OAMK-Smart-Kitchen/Smart-Fridge-OAMK/SmartKitchen-Emdebbed System/Datasheets/BL-LS1311-smd-led-lamp.gif

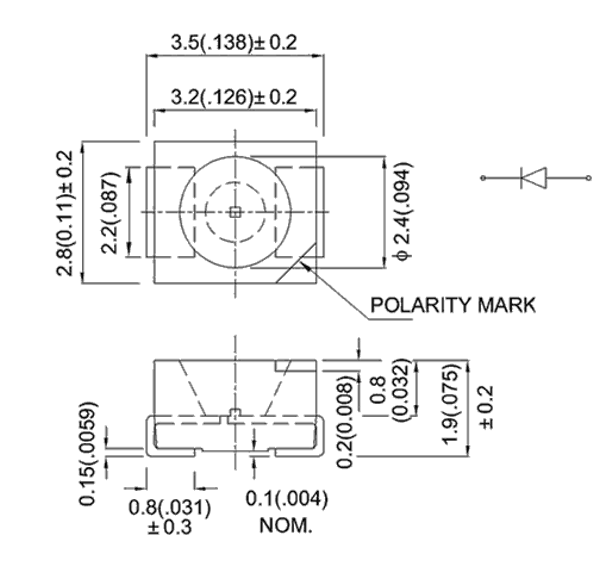
SmartKitchen-Emdebbed System/Datasheets/BL-LS1311-smd-led-lamp.gif
