OAMK-Smart-Kitchen/Smart-Fridge-OAMK/SmartKitchenApp/Documentation/Demo Screens/Dashboard_iPad_Black.png

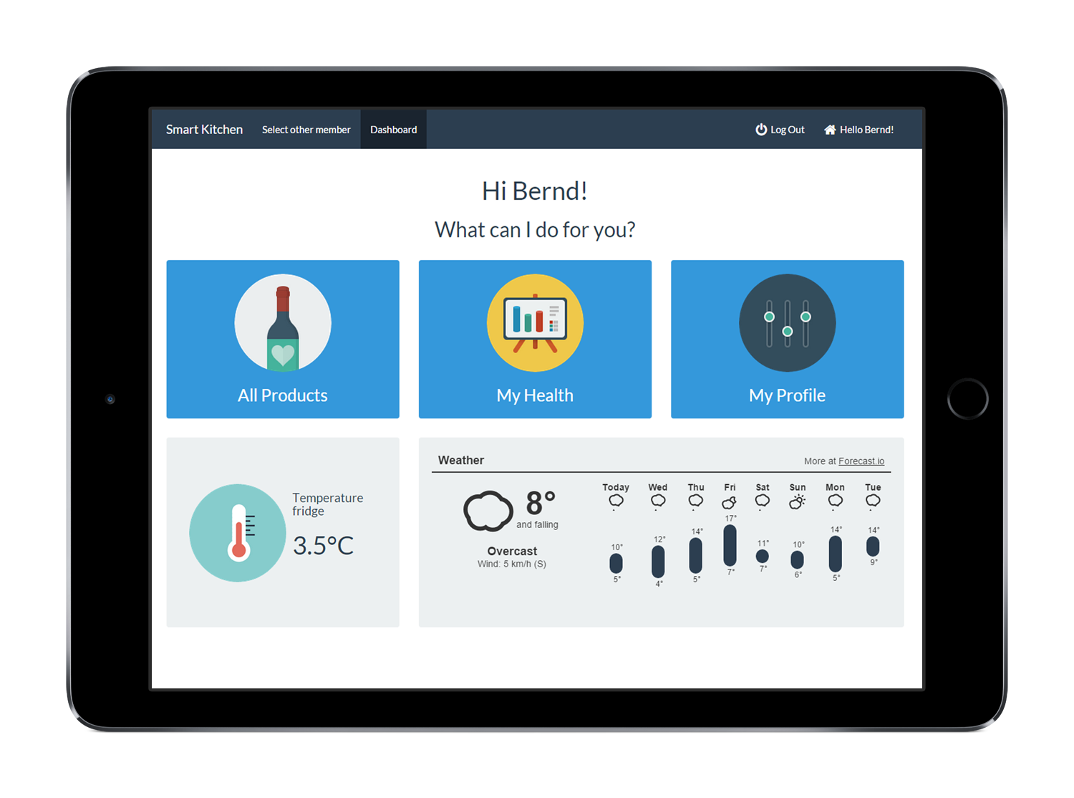
SmartKitchenApp/Documentation/Demo Screens/Dashboard_iPad_Black.png
