OAMK-Smart-Kitchen/Smart-Fridge-OAMK/SmartKitchenApp/Documentation/Demo Screens/My_Health_iPad_Black.png

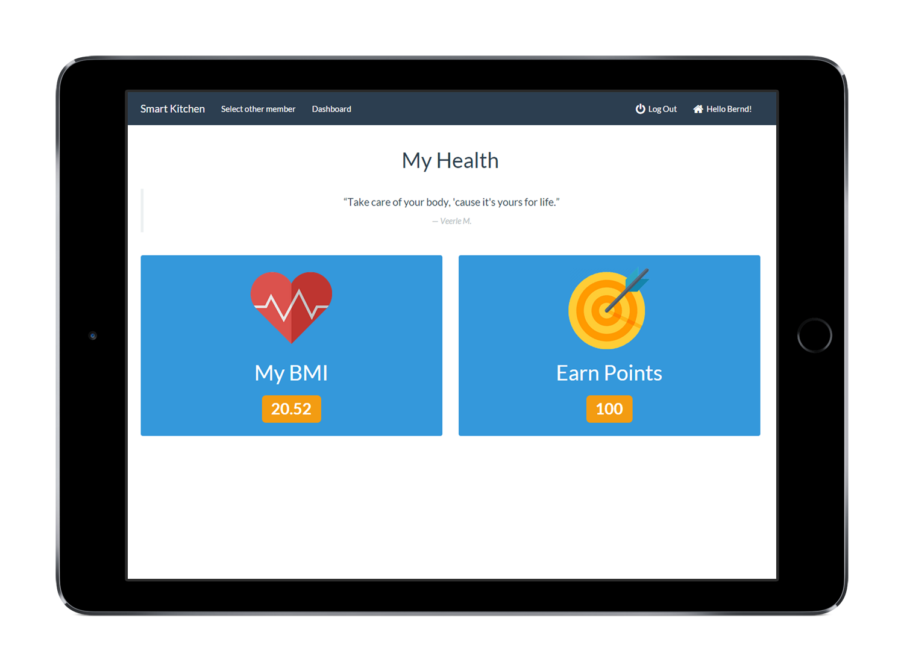
SmartKitchenApp/Documentation/Demo Screens/My_Health_iPad_Black.png
