OAMK-Smart-Kitchen/Smart-Fridge-OAMK/SmartKitchenApp/Documentation/Demo Screens/Points_iPad_Black.png

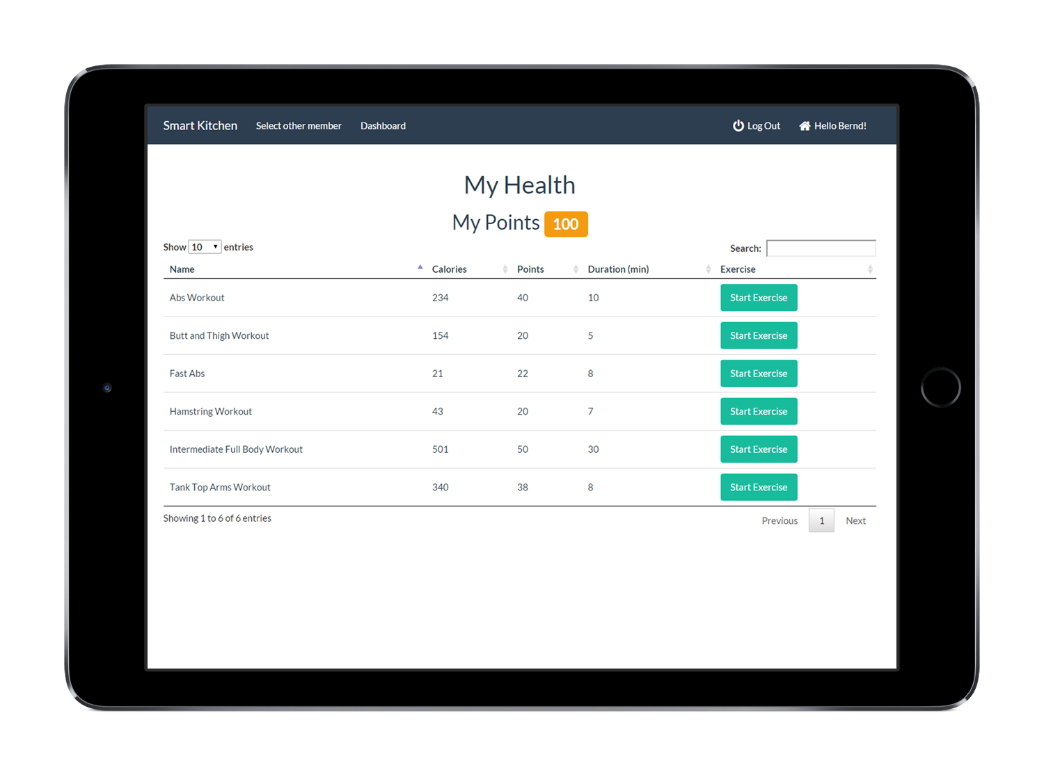
SmartKitchenApp/Documentation/Demo Screens/Points_iPad_Black.png
