OAMK-Smart-Kitchen/Smart-Fridge-OAMK/SmartKitchenApp/Documentation/Demo Screens/Workout_Video_iPad_Black.png

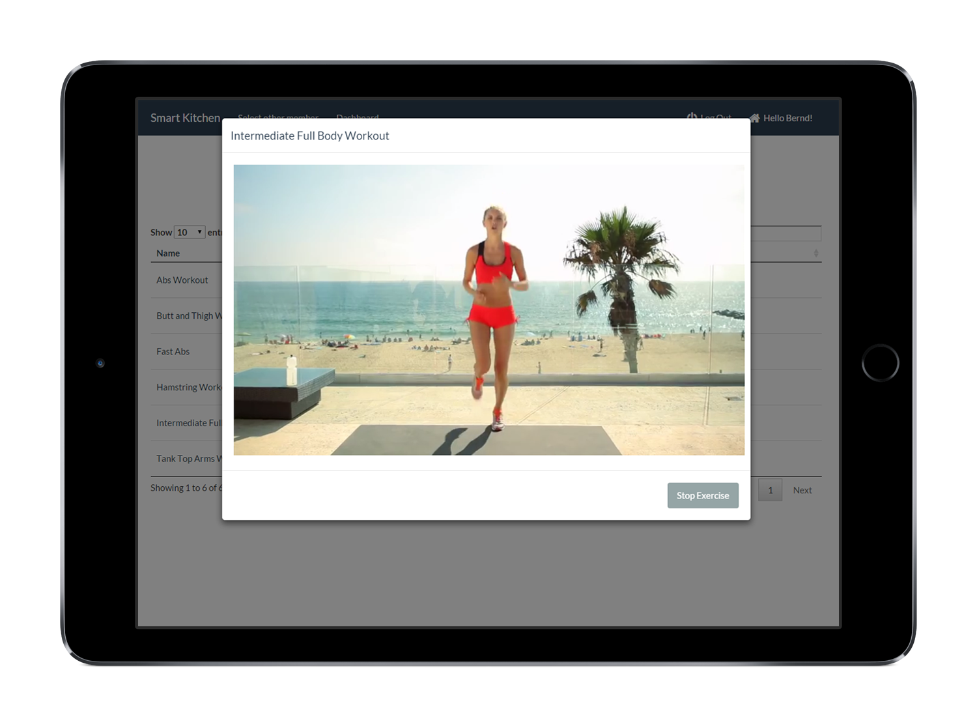
SmartKitchenApp/Documentation/Demo Screens/Workout_Video_iPad_Black.png
