OAMK-Smart-Kitchen/Smart-Fridge-OAMK/SmartKitchen-Emdebbed System/Hardware/Components/Capture.JPG

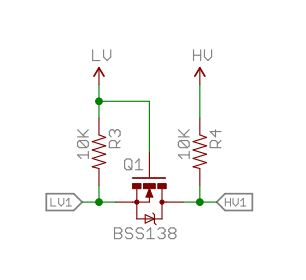
SmartKitchen-Emdebbed System/Hardware/Components/Capture.JPG
