OAMK-Smart-Kitchen/Smart-Fridge-OAMK/SmartKitchen-Emdebbed System/Software/Arduino/CommunicationtestARD/Test with SoftSerial/Test_Softserial_write.ino/Test_Softserial_write.ino.ino

/*
Uses a FOR loop for data and prints a number in various formats.
*/
int x = 0;    // variable

void setup() {
  Serial.begin(9600);      // open the serial port at 9600 bps:    
}

void loop() {  
  // print labels 
  Serial.print("XD48525352706548656557515256481310DA14ABtrueBX"); // a = 97 b = 98

  
    delay(200);            // delay 200 milliseconds

}
