OAMK-Smart-Kitchen/Smart-Fridge-OAMK/SmartKitchen-Emdebbed System/Software/Arduino/I2C_Tests/Working_I2C_2xPCF/Working_I2C_2xPCF.ino

#include <Wire.h>
 
byte iInput=0;
byte iOutput=0;
 
void setup()
{
  Wire.begin();
  Serial.begin(9600);
   pinMode(13, OUTPUT);
}
 
void loop()
{
  Wire.requestFrom(57,1);// Begin transmission to PCF8574 with the buttons (address: 111001)
  if(Wire.available())   // If bytes are available to be recieved
  {
    iInput = Wire.read();// Read a byte
    Serial.println(iInput);
  }
 
  if(iInput<=255)         //If the value less than 255
  {
    
    if (iInput==254) // P0
    { 
      iOutput = 1; 
    }; 
    if (iInput==253) // P1
    { 
      iOutput = 2; 
    }; 
    if (iInput==251) // P2
    { 
      iOutput = 4; 
    }; 
    if (iInput==247) // P3
    { 
      iOutput = 9; 
    };
    if (iInput==222) // P3
    { 
      iOutput = 9; 
    };
    
  }
  Wire.beginTransmission(56);  //Begin transmission to PCF8574 (with the LEDs)(address: 111000)
  Wire.write(iOutput);         //Send data to PCF8574 (with the LEDs)
  Serial.println(iOutput);
  Wire.endTransmission();      //End Transmission to PCF8574 (with the LEDs)
  //digitalWrite(13, HIGH);   // turn the LED on (HIGH is the voltage level)
  //iOutput = 0;
}
