OAMK-Smart-Kitchen/Smart-Fridge-OAMK/SmartKitchen-Emdebbed System/Software/Arduino/Temprature_out_test/Temprature_out_test.ino

int pin = 0;
float readt;
void setup() {
pinMode(pin, INPUT);
Serial.begin(9600);

}
void loop() {
float readt = analogRead(pin);
float Kelvin = (analogRead(pin) - 903.00);
float Celsius = Kelvin-273;
float Fahrenheit=(Celsius)*(9/5)+32;

Serial.println(Kelvin);

delay(1000);
}
